KAIST-HCIL/FS-Pad/images/FS-Pad naked.JPG

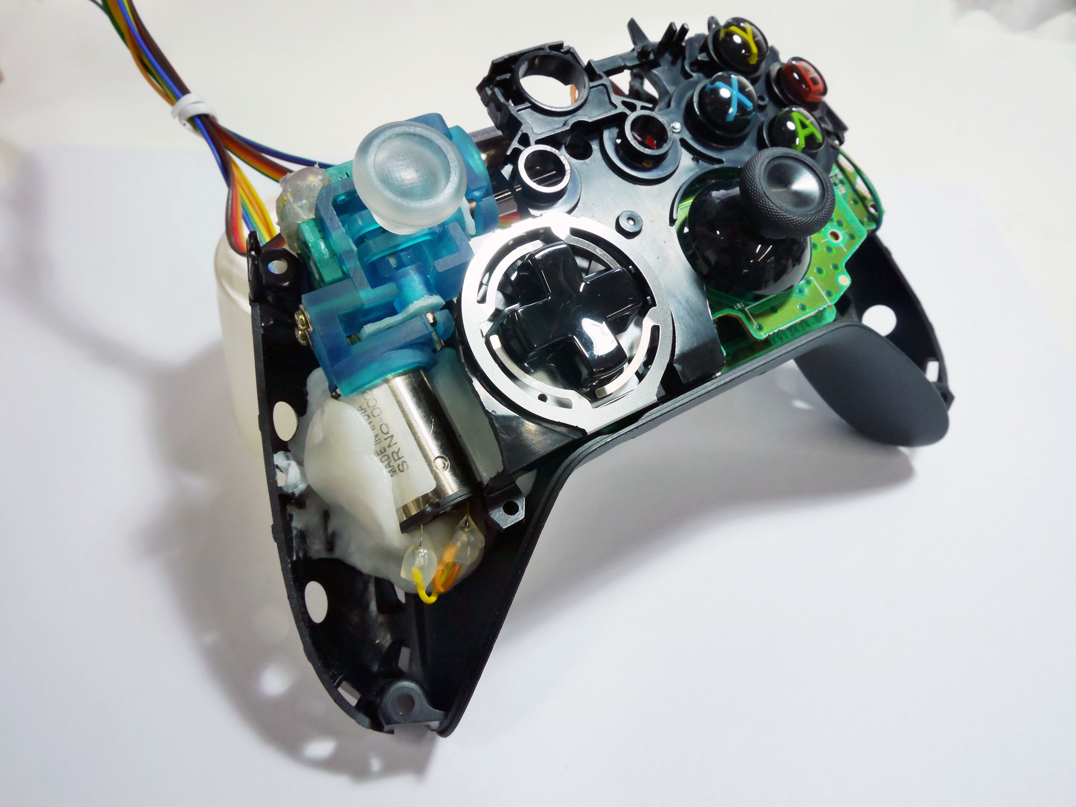
images/FS-Pad naked.JPG
