KAIST-HCIL/FS-Pad/circuitry/FSPad_sch.sch

## EAGLE design circuitry/FSPad_sch.sch (2020-06-16)

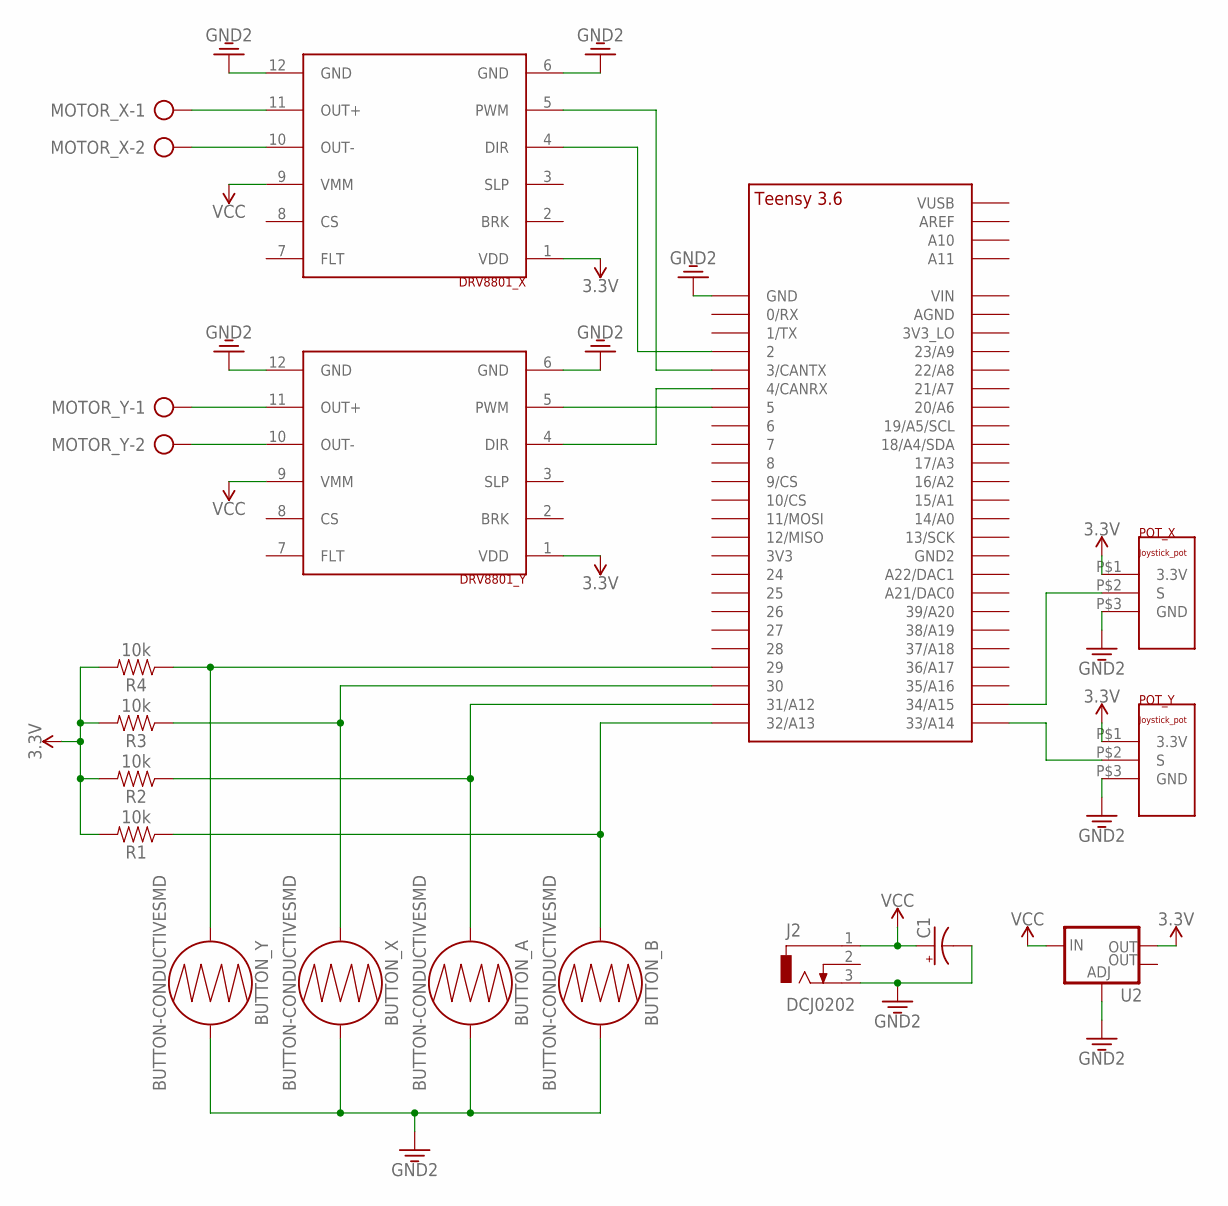
[picture p22: schematic FSPad_sch.sch]

Parts:
BUTTON_A: BUTTON-CONDUCTIVESMD; BUTTON-CONDUCTIVE
BUTTON_B: BUTTON-CONDUCTIVESMD; BUTTON-CONDUCTIVE
BUTTON_X: BUTTON-CONDUCTIVESMD; BUTTON-CONDUCTIVE
BUTTON_Y: BUTTON-CONDUCTIVESMD; BUTTON-CONDUCTIVE
C1: 1mF; CPOL-RADIAL-5MM-10MM
DRV8801_X, DRV8801_Y: DRV8801_BREAKOUT_BOARD
J2: DCJ0202
MOTOR_X: AK300/2
MOTOR_Y: AK300/2
POT_X: JOYSTICK_POT
POT_Y: JOYSTICK_POT
R1, R2, R3, R4: 10k; AXIAL-0.3
U2: V_REG_LM1117SOT223; SOT223
U$1: TEENSY_3.5/3.6_BASIC

Connections:
3.3V: BUTTON_A.2, BUTTON_B.2, BUTTON_X.2, BUTTON_Y.2, C1.-, DRV8801_X.1 (VDD), DRV8801_X.6 (GND), DRV8801_X.12 (GND), DRV8801_Y.1 (VDD), DRV8801_Y.6 (GND), DRV8801_Y.12 (GND), J2.3, POT_X.P$1 (3.3V), POT_X.P$3 (GND), POT_Y.P$1 (3.3V), POT_Y.P$3 (GND), R1.P$2 (2), R2.P$2 (2), R3.P$2 (2), R4.P$2 (2), U2.1 (ADJ), U2.2 (OUT), U$1.GND
unnamed: POT_X.P$2 (S), U$1.34/A15
unnamed: DRV8801_X.4 (DIR), U$1.2
unnamed: DRV8801_X.5 (PWM), U$1.3/CANTX
unnamed: DRV8801_Y.4 (DIR), U$1.4/CANRX
unnamed: DRV8801_Y.5 (PWM), U$1.5
unnamed: BUTTON_Y.1, R4.P$1 (1), U$1.29
unnamed: POT_Y.P$2 (S), U$1.33/A14
unnamed: BUTTON_X.1, R3.P$1 (1), U$1.30
unnamed: BUTTON_A.1, R2.P$1 (1), U$1.31/A12
unnamed: BUTTON_B.1, R1.P$1 (1), U$1.32/A13
unnamed: DRV8801_X.11 (OUT+), MOTOR_X.1
unnamed: DRV8801_X.10 (OUT-), MOTOR_X.2
unnamed: DRV8801_Y.11 (OUT+), MOTOR_Y.1
unnamed: DRV8801_Y.10 (OUT-), MOTOR_Y.2
VCC: C1.+, DRV8801_X.9 (VMM), DRV8801_Y.9 (VMM), J2.1, U2.3 (IN)
